Doubtfull/Bloom/PCB/Keeb.kicad_sch

## KiCad design PCB/Keeb.kicad_sch (2025-08-01)

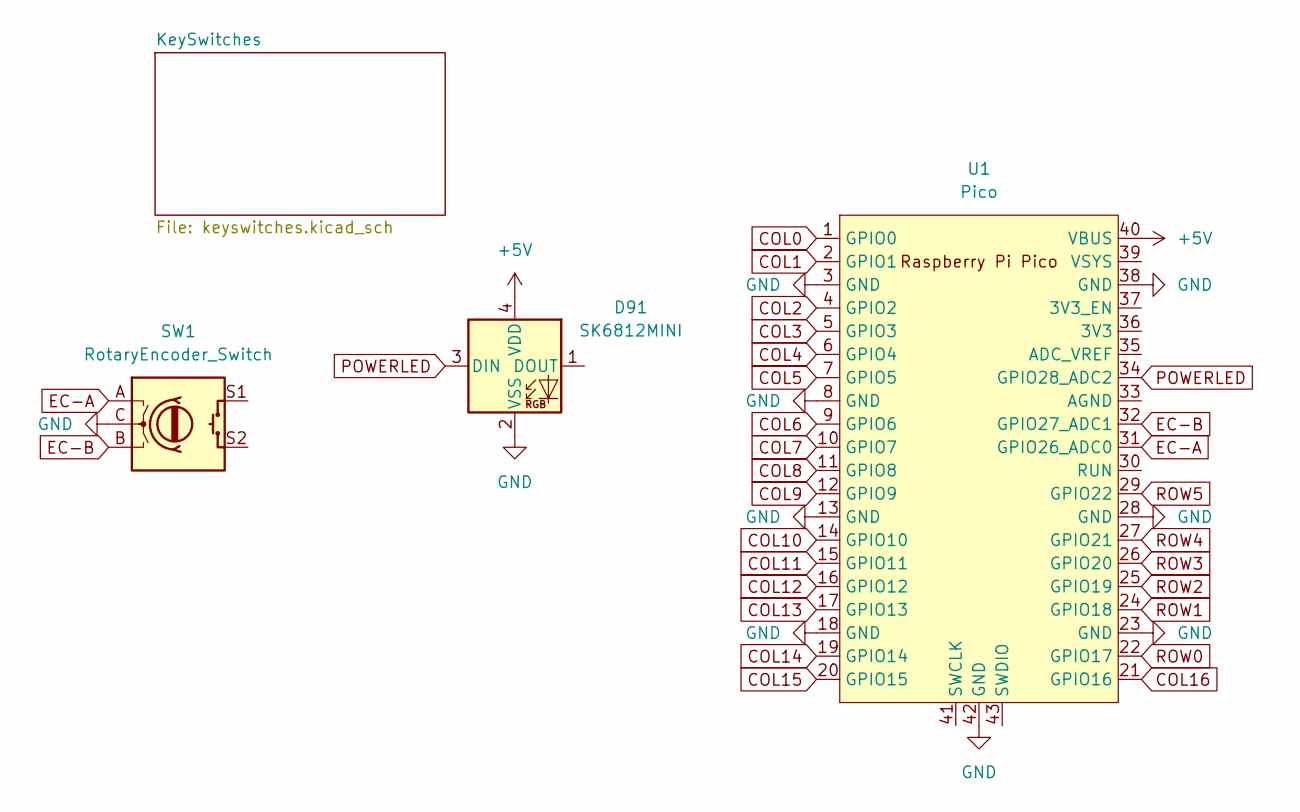
[picture p11: schematic Keeb.kicad_sch]

Parts:
D91: SK6812MINI; LED_SK6812MINI_PLCC4_3.5x3.5mm_P1.75mm
SW1: RotaryEncoder_Switch; RotaryEncoder_Alps_EC11E-Switch_Vertical_H20mm
U1: Pico; RPi_Pico_SMD_TH

Connections:
+5V: D91.4 (VDD), U1.40 (VBUS)
COL0: U1.1 (GPIO0)
COL1: U1.2 (GPIO1)
COL2: U1.4 (GPIO2)
COL3: U1.5 (GPIO3)
COL4: U1.6 (GPIO4)
COL5: U1.7 (GPIO5)
COL6: U1.9 (GPIO6)
COL7: U1.10 (GPIO7)
COL8: U1.11 (GPIO8)
COL9: U1.12 (GPIO9)
COL10: U1.14 (GPIO10)
COL11: U1.15 (GPIO11)
COL12: U1.16 (GPIO12)
COL13: U1.17 (GPIO13)
COL14: U1.19 (GPIO14)
COL15: U1.20 (GPIO15)
COL16: U1.21 (GPIO16)
EC-A: SW1.A, U1.31 (GPIO26_ADC0)
EC-B: SW1.B, U1.32 (GPIO27_ADC1)
GND: D91.2 (VSS), SW1.C, U1.3 (GND), U1.8 (GND), U1.13 (GND), U1.18 (GND), U1.23 (GND), U1.28 (GND), U1.38 (GND), U1.42 (GND)
POWERLED: D91.3 (DIN), U1.34 (GPIO28_ADC2)
ROW0: U1.22 (GPIO17)
ROW1: U1.24 (GPIO18)
ROW2: U1.25 (GPIO19)
ROW3: U1.26 (GPIO20)
ROW4: U1.27 (GPIO21)
ROW5: U1.29 (GPIO22)
